marsairforce/counter_app/Photos/IMG_0939.JPG

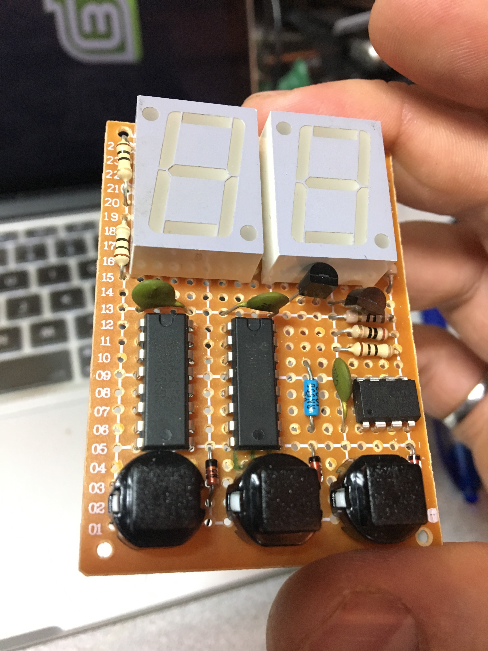
Photos/IMG_0939.JPG
