marsairforce/counter_app/Photos/IMG_1015.jpg

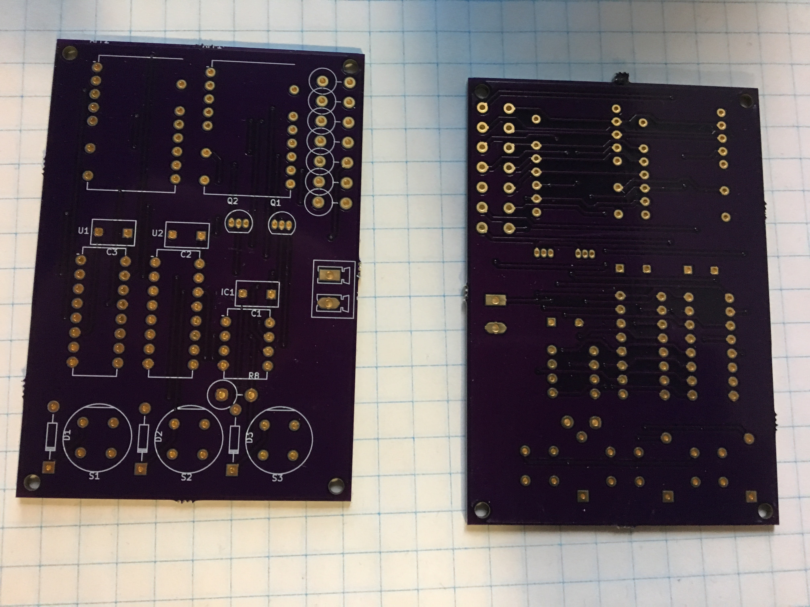
Photos/IMG_1015.jpg
