marsairforce/counter_app/Photos/IMG_1019.jpg

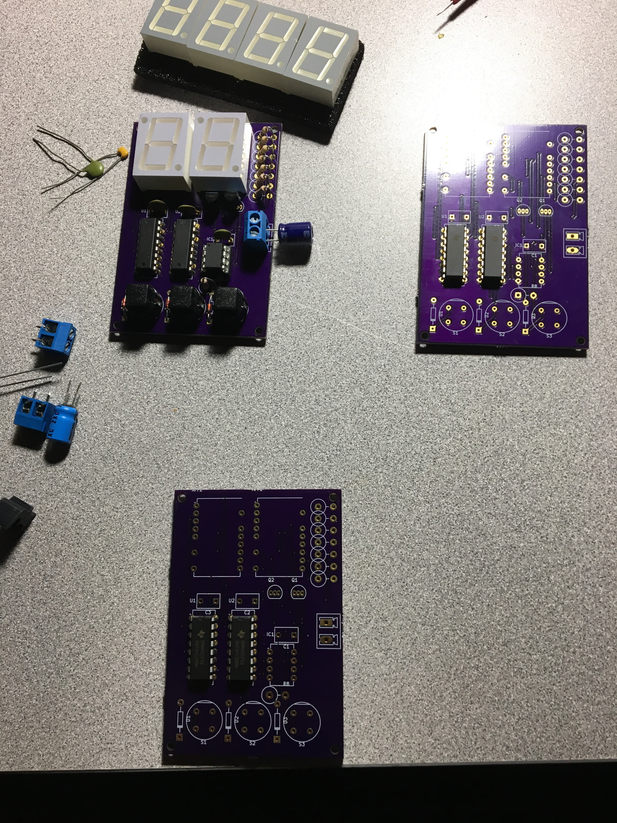
Photos/IMG_1019.jpg
