marsairforce/counter_app/Photos/IMG_1021.jpg

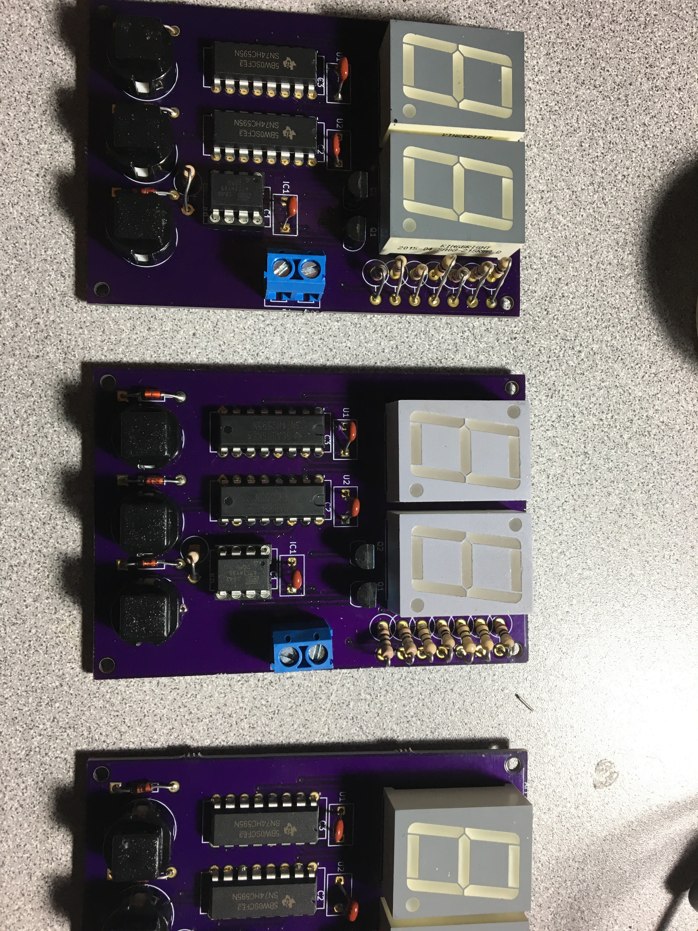
Photos/IMG_1021.jpg
