marsairforce/counter_app/Photos/IMG_1022.jpg

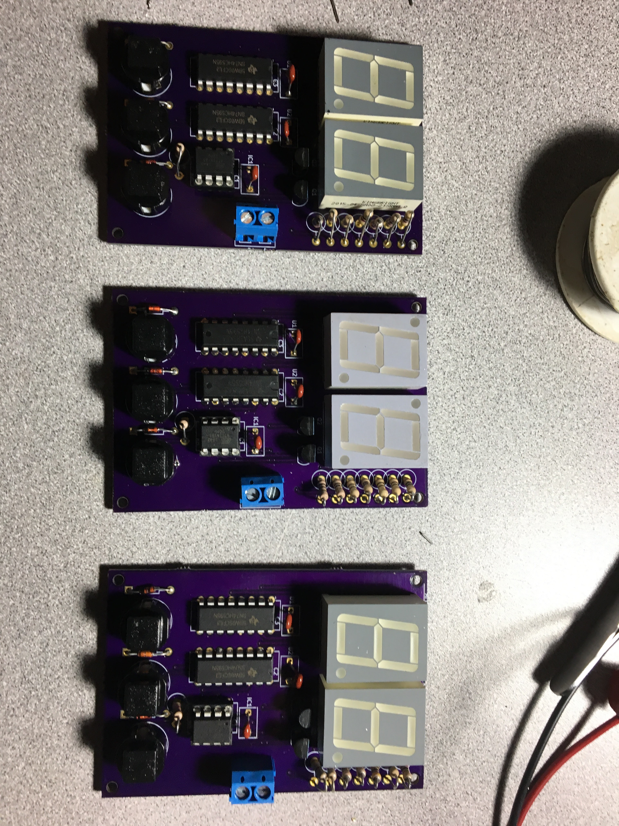
Photos/IMG_1022.jpg
